lime7git/heart/heart-software/hal-cubemx/heart-software-HAL/Core/Inc/main.h

#define LIS3DH_INT1_Pin GPIO_PIN_0
#define LIS3DH_INT1_GPIO_Port GPIOA
#define LIS3DH_INT2_Pin GPIO_PIN_1
#define LIS3DH_INT2_GPIO_Port GPIOA
#define TOUCH_BUTTON_Pin GPIO_PIN_2
#define TOUCH_BUTTON_GPIO_Port GPIOA
#define TOUCH_BUTTON_EXTI_IRQn EXTI2_3_IRQn
#define TCA6416A_RESET_Pin GPIO_PIN_6
#define TCA6416A_RESET_GPIO_Port GPIOA
