lime7git/heart/heart-software/hal-cubemx/heart-software-HAL/Drivers/TCA6416A/tca6416a.h

/**
 * @file tca6416a.h
 * @author lime7git
 * @date 16.02.2022
 * @brief GPIO expander header file
 */

/* File tca6416a  */

#ifndef __TCA6416A_H__
#define __TCA6416A_H__

/* Includes ------------------------------------------------------------------*/
#include "main.h"
#include "i2c.h"

#define TCA6416A_ADDRESS 0x20

#define TCA6416A_READ_ADDRESS 0x41
#define TCA6416A_WRITE_ADDRESS 0x40

#define TCA6416A_INPUT_PORT_0_ADDRESS 0x00
#define TCA6416A_INPUT_PORT_1_ADDRESS 0x01

#define TCA6416A_OUTPUT_PORT_0_ADDRESS 0x02
#define TCA6416A_OUTPUT_PORT_1_ADDRESS 0x03

#define TCA6416A_POLARITY_PORT_0_ADDRESS 0x04
#define TCA6416A_POLARITY_PORT_1_ADDRESS 0x05

#define TCA6416A_CONFIGURATION_0_ADDRESS 0x06
#define TCA6416A_CONFIGURATION_1_ADDRESS 0x07

/**
  * @brief  TCA6416A Texsas Instruments GPIO expander I2C slave initialization 
  * @param  None
  * @retval None
  */
HAL_StatusTypeDef TCA6416A_Initialization(void);

/**
  * @brief  TCA6416A I2C write to register
  * @param  register_address TCA6416A register to write to
  * @param  data_to_transfer pointer to data to transfer
  * @retval HAL_StatusTypeDef
  */
HAL_StatusTypeDef TCA6416A_Write(uint8_t register_address, uint8_t data_to_transfer);

/**
  * @brief  TCA6416A I2C read from register
  * @param  register_address TCA6416A register to read from
  * @param  data_received pointer to received data
  * @retval None
  */
void TCA6416A_Read(uint8_t register_address, uint8_t *data_received);

/**
  * @brief  TCA6416A set all GPIOs in Port 0 as outputs
  * @param  None
  * @retval None
  */
HAL_StatusTypeDef TCA6416A_Set_Port_0_As_Output(void);

/**
  * @brief  TCA6416A set all GPIOs in Port 1 as outputs
  * @param  None
  * @retval None
  */
HAL_StatusTypeDef TCA6416A_Set_Port_1_As_Output(void);

void TCA6416A_Disable_All_LEDs(void);
void TCA6416A_Enable_All_LEDs(void);

#endif /* __TCA6416A_H__ */
