lime7git/heart/heart-software/vs-cmsis/include/main.h

/**
 * @file main.h
 * @author lime7git
 * @date 16.02.2022
 * @brief Main header file
 */

/* File main  */
#ifndef _MAIN_H
#define _MAIN_H

#include "stm32l031xx.h"
#include "stm32l0xx.h"

#include <stdbool.h>

#include "clock.h"
#include "i2c.h"

// #include "lis3dh.h"
 #include "tca6416a.h"

#endif /* !MAIN_H */
